AllWize/AllWizeK2-hardware/RevPA/pcb/K2_RevPA_back.jpg

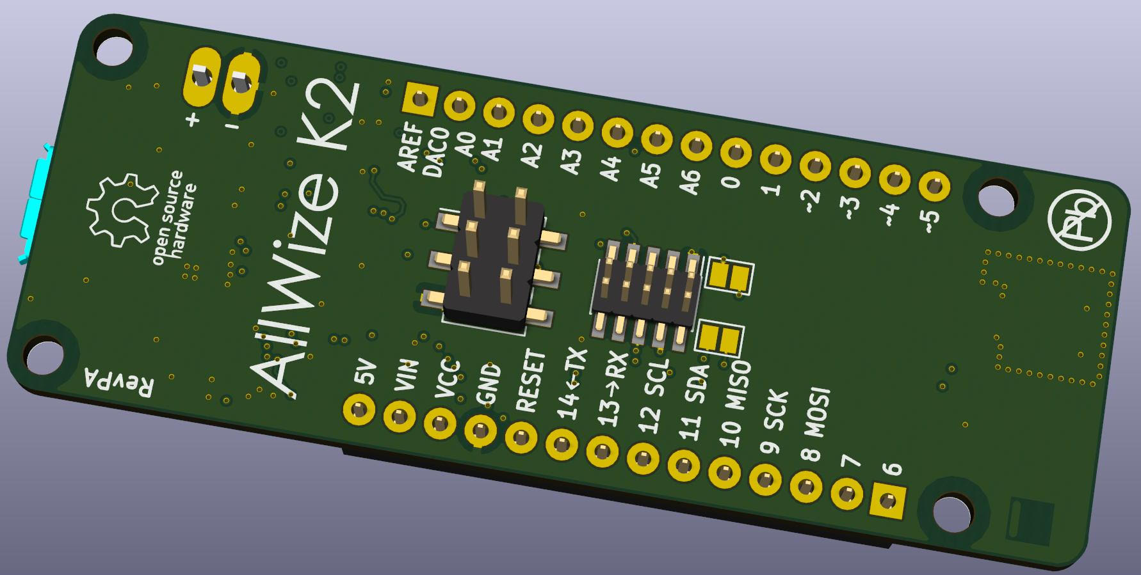
RevPA/pcb/K2_RevPA_back.jpg
